sparkfun/SparkFun_Qwiic_OLED-0.91/docs/assets/img/LCD-24606-Qwiic-OLED-Display-Arduino_RedBoard_Plus.jpg

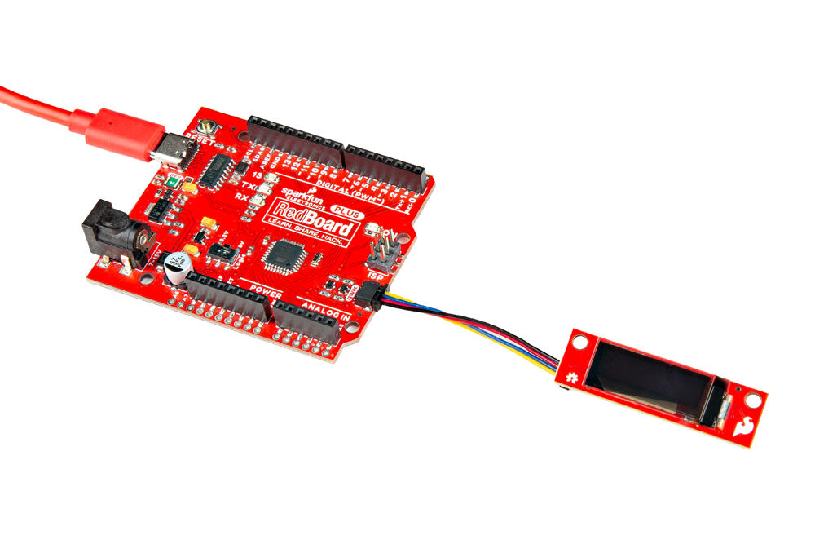
docs/assets/img/LCD-24606-Qwiic-OLED-Display-Arduino_RedBoard_Plus.jpg
