sparkfun/SparkFun_Qwiic_OLED-0.91/docs/assets/img/LCD-24606-Qwiic-OLED-Display_Enclosure_Mounted.jpg

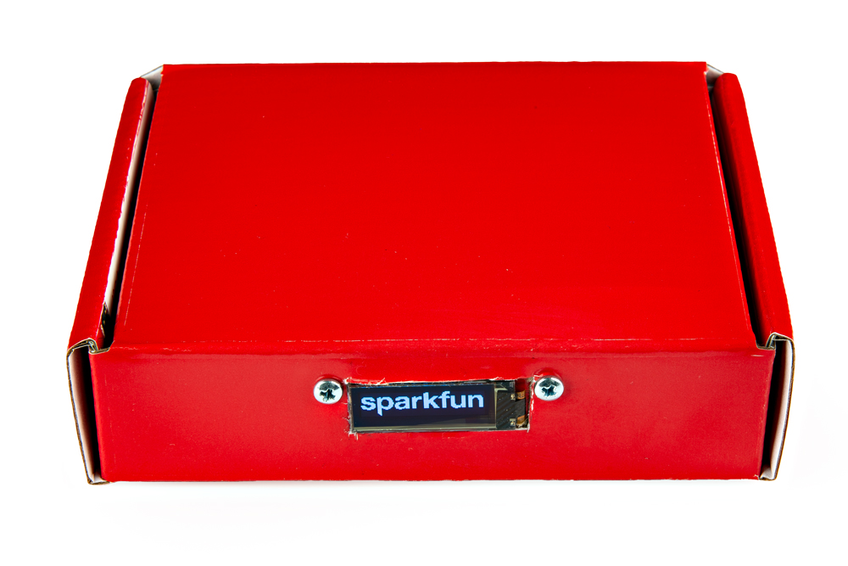
docs/assets/img/LCD-24606-Qwiic-OLED-Display_Enclosure_Mounted.jpg
